SP3WRO/APRS_Display_System/photos/2.jpg

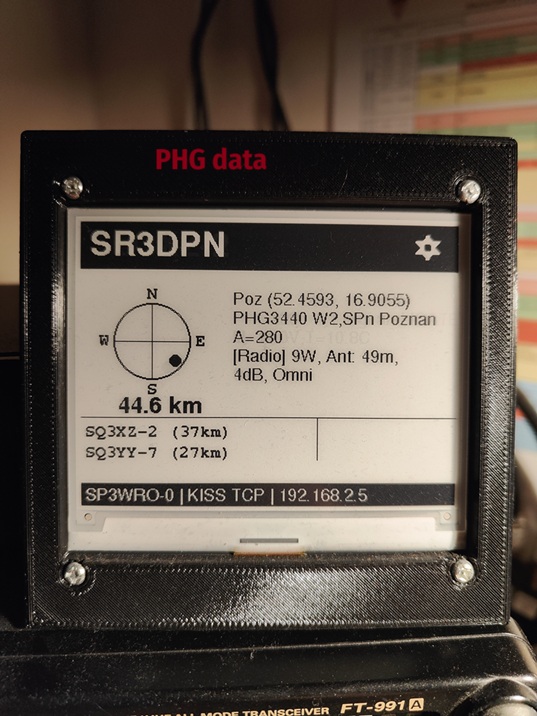
photos/2.jpg
