SP3WRO/APRS_Display_System/photos/3.jpg

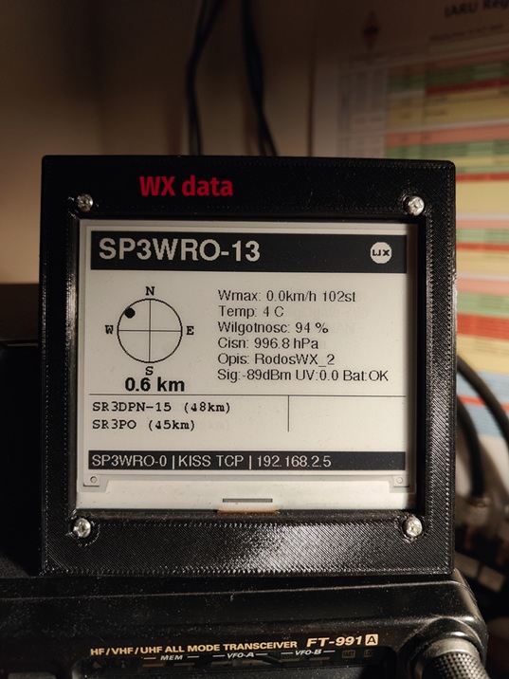
photos/3.jpg
