SP3WRO/APRS_Display_System/photos/4.jpg

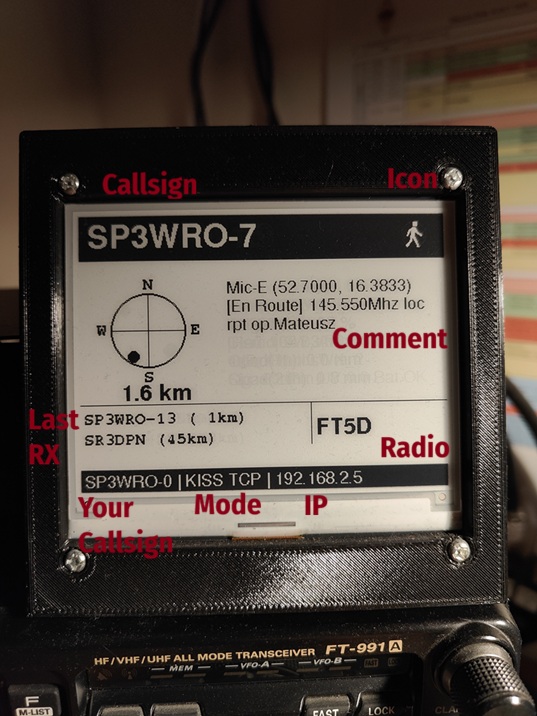
photos/4.jpg
