SP3WRO/APRS_Display_System/photos/5.png

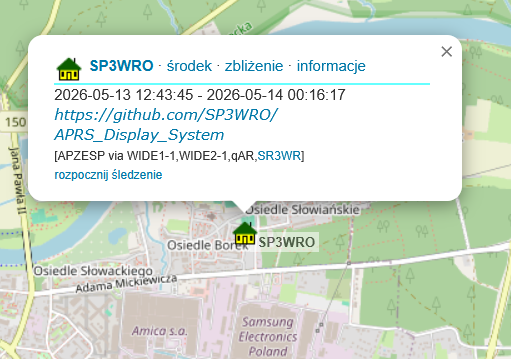
photos/5.png
