SP3WRO/APRS_Display_System/photos/7.jpg

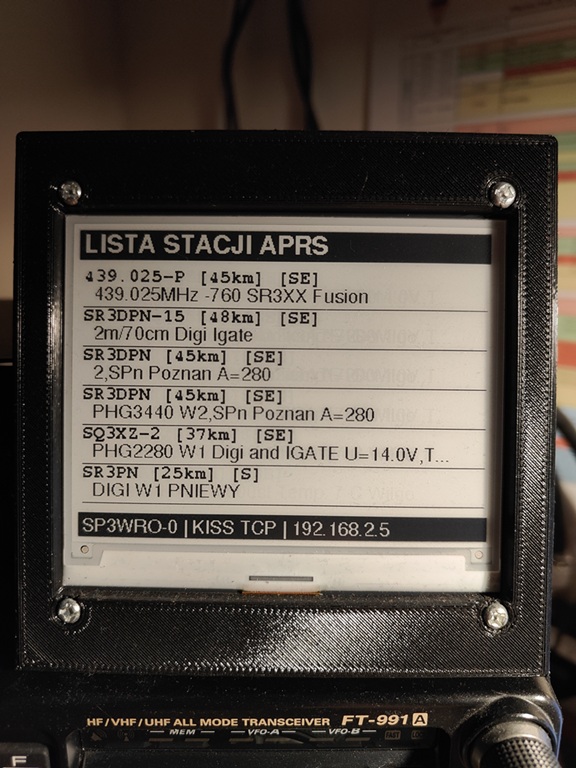
photos/7.jpg
