SP3WRO/APRS_Display_System/photos/8.jpg

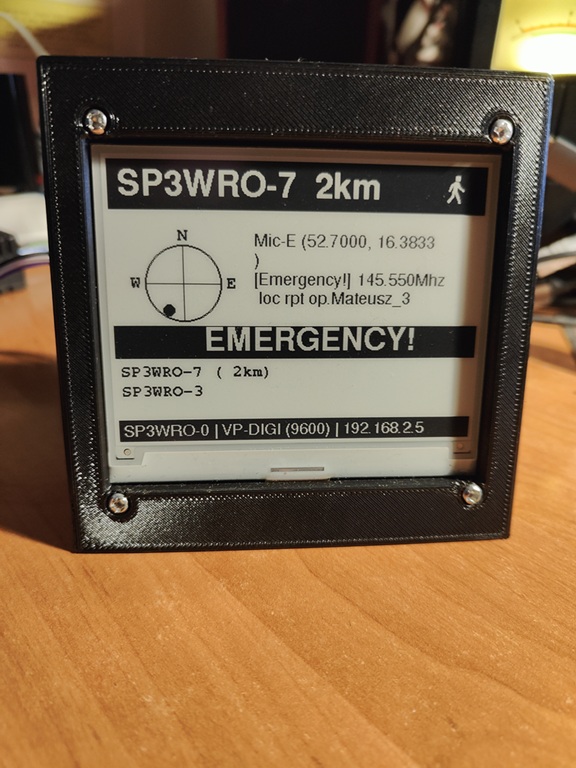
photos/8.jpg
