SP3WRO/APRS_Display_System/photos/9.jpg

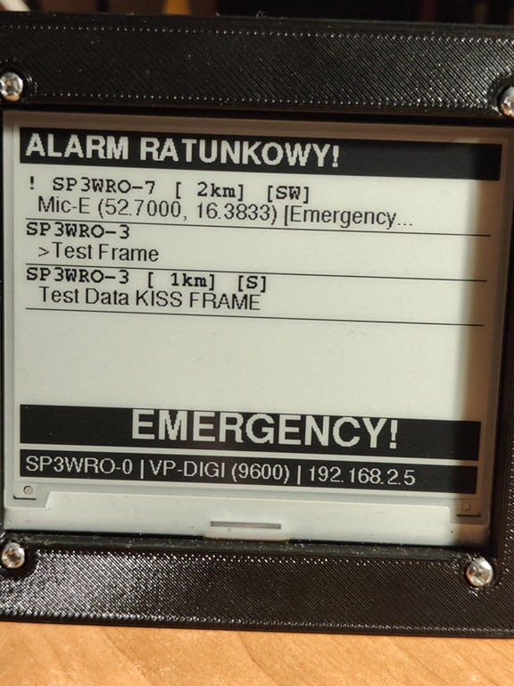
photos/9.jpg
