SP3WRO/APRS_Display_System/photos/10.jpg

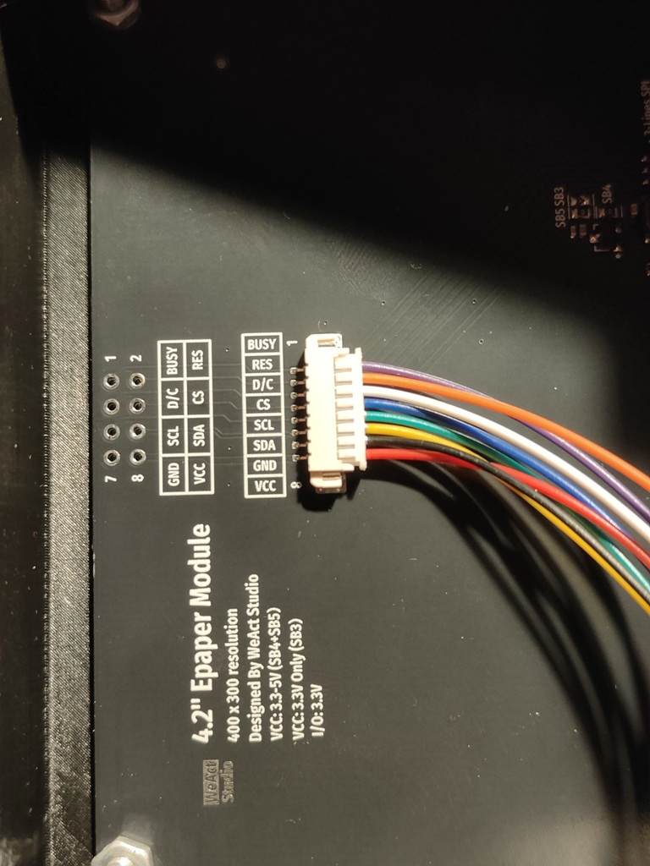
photos/10.jpg
