SP3WRO/APRS_Display_System/photos/11.jpg

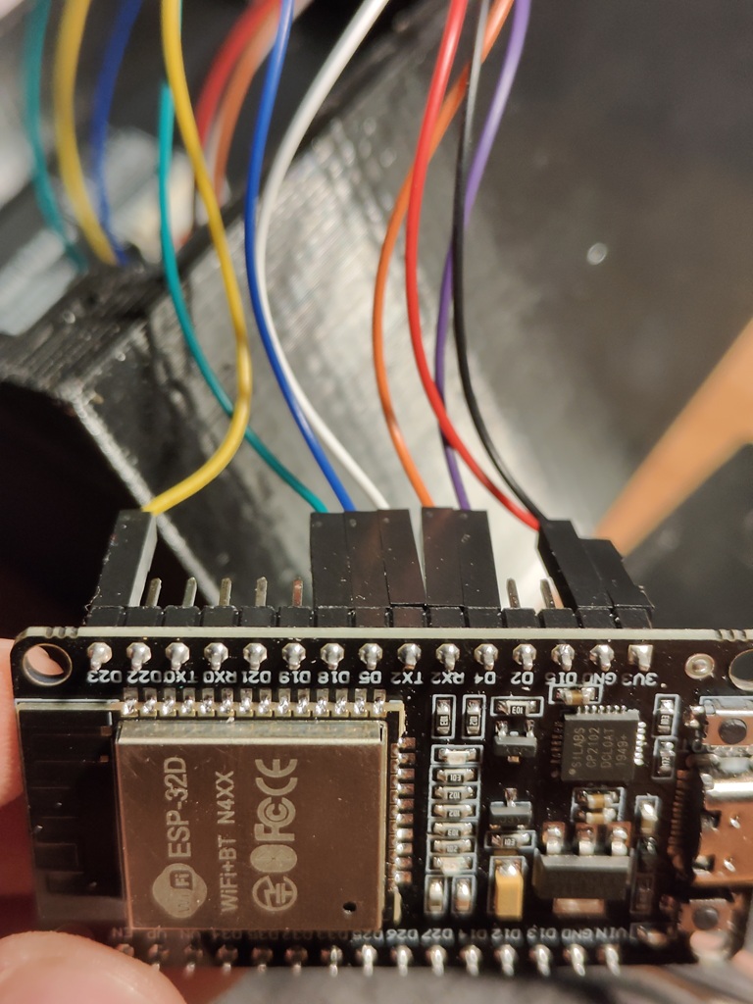
photos/11.jpg
