SP3WRO/APRS_Display_System/photos/12.jpg

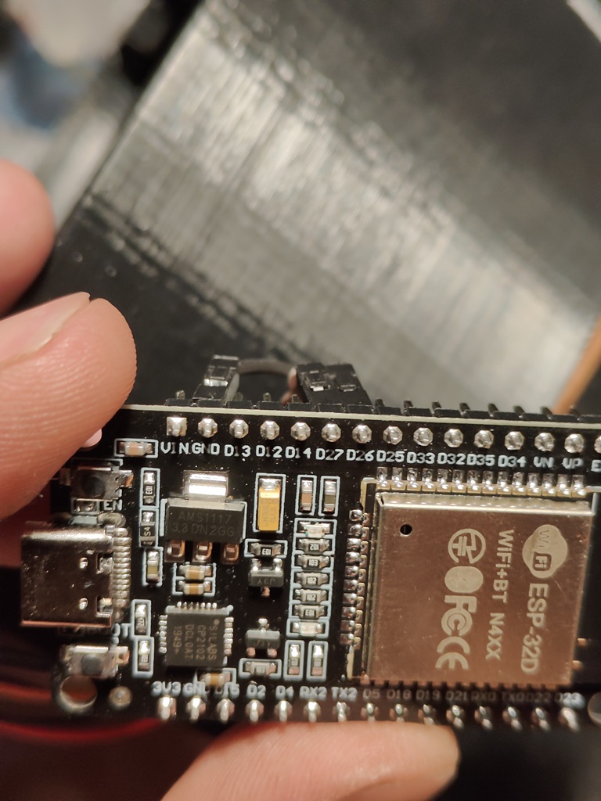
photos/12.jpg
